Hecate946/reed-case/src/parts/reed_plate.scad

/*
  Parametric implementation of the double-sided tray disclosed in
  US12103755B2, particularly Figs. 1-10 and claims 1-16.

  The patent does not disclose millimeter dimensions. The topology below
  follows the disclosure; dimensions are fitted to the configured reed and
  humidity-pack envelopes in config.scad.

  One complete tray is modeled from two reed faces and one core; the library
  exporter can fuse those regions into one permanently assembled print.
*/

include <../lib/geometry.scad>
include <../lib/hardware.scad>

// i=0 and i=reeds_per_face are virtual passage boundaries supplied by the
// structural side borders, not separate divider walls. Only indices 1..N-1
// have a physical 1.10 mm guide. This removes the redundant outer divider on
// each side and moves the edge wall inward by exactly its former thickness.
function guide_t(i) = i == 0 || i == reeds_per_face ? 0 : tray_guide_t;
function guide_x(i) = i == 0
                    ? -tray_passage_field_w / 2
                    : i == reeds_per_face
                    ? tray_passage_field_w / 2
                    : -tray_passage_field_w / 2 +
                      i * reed_slot_clear_w +
                      (i - 0.5) * tray_guide_t;
function lane_x(i) = -tray_passage_field_w / 2 +
                     reed_slot_clear_w / 2 +
                     i * (reed_slot_clear_w + tray_guide_t);
function aperture_column_pitch() = min(tray_air_column_pitch,
                                       reed_slot_clear_w / 3.7);
// The reed heel line, and therefore the tip stop, is now referenced directly
// to the tray edge. The aperture field is derived from those two lines rather
// than the other way round, which is what lets the field run nearly the full
// passage length as it does in the reference photographs.
// The reed is located from the tip border inwards. The border is a wall of
// tray_border_w sitting at the tray edge, matching the two side frames, so
// the tip end reads as the same narrow band they do instead of a wide flat
// lip. Slack collects at the open heel end, which is where you reach in to
// lift a reed out anyway.
function tip_stop_outer_y() = tray_d / 2;
function tip_stop_inner_y() = tip_stop_outer_y() - tray_border_w;
function reed_heel_y() = tip_stop_inner_y() - reed_length - reed_tip_clearance;
function aperture_edge_relief_r() = tray_air_hole_d / 2 +
                                    tray_air_edge_relief;
function aperture_start_y() = -tray_d / 2 + aperture_heel_margin +
                              aperture_edge_relief_r();
function aperture_end_y() = tip_stop_inner_y() - aperture_tip_margin -
                            aperture_edge_relief_r();
function aperture_row_pitch() = (aperture_end_y() - aperture_start_y()) /
                                max(tray_air_rows - 1, 1);
function aperture_y(row) = aperture_start_y() + row * aperture_row_pitch();
function rail_start_y() = aperture_start_y() - aperture_row_pitch() / 2;
function rail_end_y() = (aperture_y(rail_rows - 1) +
                         aperture_y(rail_rows)) / 2;
function reed_plane_front_y() = aperture_start_y() -
                                 tray_air_hole_d / 2 -
                                 tray_air_edge_relief -
                                 tray_reed_plane_edge_margin;
// Digits sit centred on the height of the tip-stop wall.
function lane_number_z() = tray_face_t + tray_guide_h / 2;
function reed_center_y() = (reed_heel_y() + tip_stop_inner_y()) / 2;
function guide_wall_start_y() = guide_walls_full_length
                              ? -tray_d / 2 - epsilon
                              : reed_plane_front_y();
function ventilation_field_half_w() =
    abs(lane_x(0)) +
    (tray_air_columns - 1) / 2 * aperture_column_pitch() +
    (tray_air_hole_d + 2 * tray_air_edge_relief) / 2 +
    tray_pack_vent_clearance;

// If both optional features are switched back on at once, the rails can start
// ahead of the sheet and print as detached islands. The margin is small even
// at the default row count, so fail loudly rather than ship floating rails.
assert(!(stock_rails_enable && front_plane_cutout_enable) ||
       rail_start_y() >= reed_plane_front_y() + 0.50,
       str("Stock rails would begin ", reed_plane_front_y() - rail_start_y(),
           " mm ahead of the reed-facing sheet. Increase tray_air_rows, ",
           "reduce tray_reed_plane_edge_margin, or leave ",
           "front_plane_cutout_enable off."));

module patent_face_outline_2d() {
    // A plain rounded rectangle. The magnet pockets are buried inside the
    // side borders now, so there are no ears protruding past this outline.
    offset(r = tray_body_corner_r)
        square([tray_body_w - 2 * tray_body_corner_r,
                tray_d - 2 * tray_body_corner_r], center = true);
}

module patent_platform(h) {
    linear_extrude(height = h) patent_face_outline_2d();
}

module patent_ventilation_apertures_2d(hole_d = tray_air_hole_d) {
    // Physical tray: 22 rows of three small apertures in each passage.
    for (i = [0 : reeds_per_face - 1],
         row = [0 : tray_air_rows - 1],
         col = [0 : tray_air_columns - 1]) {
        x_offset = (col - (tray_air_columns - 1) / 2) *
                   aperture_column_pitch();
        translate([lane_x(i) + x_offset, aperture_y(row)])
            circle(d = hole_d, $fn = is_library_fdm ? 16 : ($preview ? 16 : 24));
    }
}

module patent_front_plane_cutout_2d() {
    // Optional. The reference tray edge is solid above and below the humidity
    // pack mouth, so this is disabled by default; set
    // front_plane_cutout_enable = true in config.scad to restore the open
    // insertion end. The outer-frame strips and corner ears stay full length
    // for stiffness either way.
    if (front_plane_cutout_enable) {
        left_inner_x = guide_x(0) + guide_t(0) / 2;
        right_inner_x = guide_x(reeds_per_face) -
                        guide_t(reeds_per_face) / 2;
        front_y = -tray_d / 2 - epsilon;
        back_y = reed_plane_front_y();

        assert(back_y > -tray_d / 2,
               "Reed-plane margin extends beyond the tray outline");

        translate([(left_inner_x + right_inner_x) / 2,
                   (front_y + back_y) / 2])
            square([right_inner_x - left_inner_x,
                    back_y - front_y], center = true);
    }
}

module patent_lane_number_engraving(first_lane = 1) {
    // Engraved passage numbers on the vertical inner face of the reed tip
    // stop, one per passage, reading upright when the open tray is viewed
    // from the heel end.
    //
    // rotate([90, 0, 0]) maps the glyph's own +x onto world +X and its +y
    // onto world +Z, which is what an observer at -Y reads as left-to-right
    // and upright. That same rotation sends the extrusion to -Y, so the
    // block is placed one depth proud of the wall and cuts back into it.
    if (lane_numbers_enable)
        for (i = [0 : reeds_per_face - 1])
            translate([lane_x(i),
                       tip_stop_inner_y() + lane_number_depth,
                       lane_number_z()])
                rotate([90, 0, 0])
                    linear_extrude(height = lane_number_depth + epsilon)
                            text(str(i + first_lane),
                                 size = lane_number_size,
                                 font = lane_number_font,
                                 halign = "center",
                                 valign = "center",
                                 $fn = is_library_fdm ? 16 : ($preview ? 16 : 32));
}

module patent_perforated_layer(z, h, hole_d, outline_inset = 0) {
    // Keep the perforations as ordinary 2D boolean holes before extrusion.
    // This is substantially faster and more reliable in OpenSCAD 2021 than
    // encoding hundreds of hole loops into one giant polygon path.  It also
    // produces a normal slicer-friendly manifold instead of spending minutes
    // in CGAL triangulation during each STL export.
    translate([0, 0, z])
        linear_extrude(height = h, convexity = 10)
            difference() {
                offset(delta = -outline_inset) patent_face_outline_2d();
                patent_ventilation_apertures_2d(hole_d);
                patent_front_plane_cutout_2d();
            }
}

module patent_perforated_platform() {
    // Production keeps the tiny stepped relief around every ventilation hole.
    // A 0.18 mm rim relief is below what a typical 0.4 mm-nozzle library FDM
    // printer can reproduce consistently, while it makes OpenSCAD 2021 spend
    // several extra minutes unioning hundreds of tiny loops.  The library
    // profile therefore exports the SAME 1.60 mm functional holes as one flat
    // sheet.  Nothing affecting reed, Boveda, band, or magnet fit changes.
    if (is_library_fdm) {
        patent_perforated_layer(0, tray_face_t, tray_air_hole_d, 0);
    } else {
        relief_step_h = tray_air_edge_relief_h / tray_air_edge_steps;
        core_h = tray_face_t - tray_air_edge_relief_h;

        union() {
            patent_perforated_layer(0, core_h + epsilon, tray_air_hole_d, 0);
            for (step = [0 : tray_air_edge_steps - 1])
                patent_perforated_layer(
                    core_h + step * relief_step_h - epsilon,
                    relief_step_h + 2 * epsilon,
                    tray_air_hole_d + 2 * tray_air_edge_relief *
                        (step + 1) / tray_air_edge_steps,
                    tray_platform_top_chamfer *
                        (step + 1) / tray_air_edge_steps
                );
        }
    }
}

module patent_guide_walls() {
    // In the reference photographs the dividers run the whole length of the
    // tray. They are extruded as one 2D profile intersected with the tray
    // outline, so the ends follow the rounded corners instead of hanging over
    // them, and the whole set is a single cheap extrusion.
    start_y = guide_wall_start_y();
    end_y = tip_stop_inner_y() + epsilon;

    translate([0, 0, tray_face_t - tray_feature_fuse_overlap])
        union()
            // The side borders are the outer walls; only make the N-1
            // dividers that actually separate adjacent reed passages.
            for (i = [1 : reeds_per_face - 1])
                intersection() {
                    linear_extrude(height = tray_guide_h + tray_feature_fuse_overlap)
                        patent_face_outline_2d();
                    top_chamfered_extrude(tray_guide_h + tray_feature_fuse_overlap,
                                          tray_wall_top_chamfer)
                        translate([guide_x(i), (start_y + end_y) / 2])
                            square([guide_t(i), end_y - start_y],
                                   center = true);
                }
}

module patent_guide_end_runout() {
    // Cutting solid that takes every raised feature down to the floor over
    // the last guide_end_taper millimetres of the open heel end.
    //
    // The quarter-round is intentionally oriented so the visible profile is
    // tangent to the FLOOR at the open heel and turns upward into the full
    // wall inboard. This is the opposite curvature from the previous
    // prototype: instead of looking like a rounded nose dropping into the
    // opening, the wall now rises smoothly out of the reed plane.
    //
    // guide_end_taper == tray_guide_h gives a true circular quarter round.
    L = guide_end_taper;
    h = tray_guide_h;
    y0 = -tray_d / 2 - epsilon;
    z0 = tray_face_t;
    z_top = z0 + h + 1.0;
    steps = is_library_fdm ? 16 : ($preview ? 10 : 24);
    span = tray_w + 20;

    if (L > 0)
        translate([-span / 2, 0, 0])
            rotate([0, 90, 0])
                linear_extrude(height = span)
                    polygon(concat(
                        [[z0 - 1.0, y0 - 1.0], [z_top, y0 - 1.0],
                         [z_top, y0 + L]],
                        [for (s = [steps : -1 : 0])
                            let (u = s / steps)
                            [z0 + h * (1 - sqrt(max(1 - u * u, 0))),
                             y0 + L * u]],
                        [[z0 - 1.0, y0]]
                    ));
}

module patent_longitudinal_stock_rails() {
    // Fig. 4 element 152. Two rounded rails per passage, each sitting midway
    // between adjacent aperture columns so it runs tangent to the softened
    // hole rims rather than across them. They begin half a row pitch below
    // the first aperture, at the heel edge, and stop halfway between rows 11
    // and 12 - the 11.5th row - covering exactly half of the 22-row field.
    //
    // The profile is a hull of two flattened spheres, which gives a rounded
    // crown and domed ends in one cheap operation.
    end_radius = rail_w / 2;

    if (stock_rails_enable)
    for (i = [0 : reeds_per_face - 1], side = [-1, 1])
        hull()
            for (y = [rail_start_y() + end_radius,
                      rail_end_y() - end_radius])
                translate([lane_x(i) +
                           side * aperture_column_pitch() / 2,
                           y,
                           tray_face_t])
                    scale([1, 1, rail_h / end_radius])
                        sphere(d = rail_w, $fn = is_library_fdm ? 16 : ($preview ? 16 : 32));
}

module patent_reed_tip_stop() {
    // The third border. Same construction as the side frames: a plain
    // rectangle of tray_border_w, run out to the tray edge and intersected
    // with the body outline so the two ends pick up the corner radius and
    // meet the side frames in a closed U.
    inner_y = tip_stop_inner_y();

    assert(tray_border_w >= lane_number_depth + 1.0,
           "Tip border is too thin to carry the engraved numbers");

    translate([0, 0, tray_face_t - tray_feature_fuse_overlap])
        intersection() {
            linear_extrude(height = tray_guide_h + tray_feature_fuse_overlap)
                patent_face_outline_2d();
            top_chamfered_extrude(tray_guide_h + tray_feature_fuse_overlap,
                                  tray_wall_top_chamfer)
                translate([0, inner_y + tray_border_w / 2 + epsilon])
                    square([tray_body_w + 20,
                            tray_border_w + 2 * epsilon], center = true);
        }
}

module patent_outer_side_walls() {
    // The structural side frames now ARE the outer walls of lanes 1 and N.
    // Their inner faces sit exactly where the inner faces of the old outer
    // divider walls sat. That removes one redundant 1.60 mm wall per side
    // while preserving lane width, magnet protection and the rounded outline.
    passage_edge = tray_passage_field_w / 2;
    side_frame_w = tray_body_w / 2 - passage_edge;

    assert(side_frame_w > 0,
           "Passage field leaves no room for a side frame");

    translate([0, 0, tray_face_t - tray_feature_fuse_overlap])
        union()
            for (x = [-1, 1])
                intersection() {
                    linear_extrude(height = tray_guide_h + tray_feature_fuse_overlap)
                        patent_face_outline_2d();
                    top_chamfered_extrude(tray_guide_h + tray_feature_fuse_overlap,
                                          tray_wall_top_chamfer)
                        translate([x * (passage_edge +
                                        side_frame_w / 2), 0])
                            square([side_frame_w,
                                    tray_d + 2 * epsilon], center = true);
                }
}

module patent_magnet_apertures() {
    for (x = [-1, 1], y = [-1, 1])
        translate([x * tray_magnet_x, y * tray_magnet_y,
                   tray_face_t + tray_guide_h -
                   tray_magnet_h - magnet_h_clearance])
            magnet_pocket();
}

function band_groove_r() = elastic_band_d / 2 + elastic_band_clearance;
function band_groove_z() = tray_face_t + tray_guide_h -
                           band_groove_r() - elastic_band_seat_depth;
function band_y(gap) = aperture_y(gap - 1);

module patent_band_notches() {
    // A half-round seat for round elastic cord, swept across the whole tray
    // so every divider, both side borders and the tip border get the same
    // groove and the cord runs dead straight.
    //
    // The groove centre is elastic_band_seat_depth below a plain half-round,
    // so the cord sits about 70% buried and cannot roll off the wall tops,
    // while the mouth stays wider than the cord and needs no undercut.
    //
    // band_y() takes a 1-indexed row gap: 8.5 is between holes 8 and 9,
    // counting apertures from the heel end.
    for (gap = elastic_band_row_gaps) {
        translate([-tray_w / 2 - epsilon, band_y(gap), band_groove_z()])
            rotate([0, 90, 0])
                cylinder(r = band_groove_r(),
                         h = tray_w + 2 * epsilon,
                         $fn = is_library_fdm ? 20 : ($preview ? 24 : 48));
        // Square off everything above the seat so the mouth is open to the
        // top face instead of leaving a lip the cord has to snap past.
        translate([0, band_y(gap),
                   band_groove_z() + (tray_guide_h + 1) / 2])
            cube([tray_w + 2 * epsilon,
                  2 * band_groove_r(),
                  tray_guide_h + 1], center = true);
    }
}

module patent_pack_stop_ribs() {
    // Full-height humidity-pack stop ribs live in the CENTER CORE, not on the
    // printable reed faces. This is deliberately a printability feature:
    // face A and face B now have completely flat backs at Z=0 and can be
    // printed reed-side-up directly on the build plate with no supports.
    //
    // The ribs start at the heel bridge, so they are fused to the U-shaped
    // core and cannot become loose islands. Their final volume is identical
    // to the two old half-ribs after assembly; it is simply assigned to the
    // support-friendly part instead.
    rib_start_y = -tray_d / 2;
    rib_end_y = tray_pack_stop_y;
    rib_length = rib_end_y - rib_start_y;

    for (i = [1 : reeds_per_face - 1])
        translate([guide_x(i), (rib_start_y + rib_end_y) / 2,
                   tray_core_h / 2])
            cube([tray_pack_support_w, rib_length,
                  tray_core_h], center = true);
}

module behn_tray_face(first_lane = 1) {
    union() {
        patent_perforated_platform();
        difference() {
            union() {
            patent_guide_walls();
            patent_outer_side_walls();
            patent_longitudinal_stock_rails();
            patent_reed_tip_stop();
            }
            patent_guide_end_runout();
            patent_band_notches();
            patent_magnet_apertures();
            patent_lane_number_engraving(first_lane);
        }
    }
}

module behn_tray_core() {
    // The channel is wide enough to expose even the outer edges of the
    // chamfered ventilation holes, not merely wide enough for the pack.
    cavity_w = max(boveda_w + 2 * boveda_clearance,
                   2 * ventilation_field_half_w());
    side_rail_w = (tray_body_w - cavity_w) / 2;
    mouth_cap_r = side_rail_w / 2;
    cavity_start_y = -tray_d / 2 + tray_core_heel_bridge_d;
    cap_center_y = tray_d / 2 - mouth_cap_r;

    assert(side_rail_w >= tray_core_side_wall_min,
           "Humidity channel leaves too little material in the core side rails");
    assert(cap_center_y > cavity_start_y,
           "Core is too short for a semicircular humidity-pack mouth cap");

    // Build the core positively as a U-frame instead of subtracting circular
    // bites from a rectangular frame.  Each open leg therefore terminates in
    // a TRUE SEMICIRCULAR CAP: the outer and inner edges have the same radius
    // and flow continuously into one another, like ().  This avoids the old
    // concave 'bite taken out of the corner' appearance at the pack mouth.
    union() {
        linear_extrude(height = tray_core_h, convexity = 10)
            intersection() {
                patent_face_outline_2d();
                union() {
                // Narrow heel bridge keeps the core one connected print.
                translate([0,
                           -tray_d / 2 + tray_core_heel_bridge_d / 2])
                    square([tray_body_w,
                            tray_core_heel_bridge_d], center = true);

                // Two straight rails with pill/semicircular open ends.
                for (side = [-1, 1]) {
                    rail_x = side * (cavity_w / 2 + side_rail_w / 2);

                    // Straight portion; overlaps the heel bridge slightly so
                    // the exported STL is unequivocally one fused solid.
                    translate([rail_x,
                               (cavity_start_y + cap_center_y) / 2])
                        square([side_rail_w,
                                cap_center_y - cavity_start_y + 2 * epsilon],
                               center = true);

                    // Equal-radius cap on both sides of the rail end.
                    translate([rail_x, cap_center_y])
                        circle(r = mouth_cap_r,
                               $fn = is_library_fdm ? 32 : ($preview ? 32 : 64));
                }
                }
            }

        // The full-height pack-stop ribs are part of this flat-printing core.
        patent_pack_stop_ribs();
    }
}

// Passages 1..N. Hardware pockets are identical to face B.
module behn_tray_face_a() { behn_tray_face(1); }

// Passages N+1..2N. Geometry matches face A except for numbering; the final
// magnet/steel assignment is intentionally not encoded in the printed part.
module behn_tray_face_b() { behn_tray_face(reeds_per_face + 1); }

// Positive overlap used only by the monolithic export. The three-piece
// construction can meet at exact planes, but a one-piece STL should contain
// actual shared volume so slicers cannot interpret the interfaces as shells.
tray_monolithic_fuse = 0.15;

module behn_tray_interface_fusers(overlap = tray_monolithic_fuse) {
    // Copy a thin slice of the core through each mating face. These slices
    // occupy material that is already inside the face sheets, so they create
    // a true boolean union without changing the external dimensions or the
    // Boveda opening.
    translate([0, 0, -overlap])
        intersection() {
            behn_tray_core();
            translate([-tray_body_w, -tray_d, 0])
                cube([2 * tray_body_w, 2 * tray_d, overlap]);
        }

    translate([0, 0, overlap])
        intersection() {
            behn_tray_core();
            translate([-tray_body_w, -tray_d, tray_core_h - overlap])
                cube([2 * tray_body_w, 2 * tray_d, overlap]);
        }
}


module behn_tray_core_monolithic() {
    // Same XY geometry as the normal core, extended 0.15 mm into each face.
    // This does NOT narrow the Boveda tunnel; only the solid core rails/ribs
    // enter the face sheets. The overlap guarantees the one-file library STL
    // slices as one permanently fused physical part.
    translate([0, 0, -tray_monolithic_fuse])
        scale([1, 1,
               (tray_core_h + 2 * tray_monolithic_fuse) / tray_core_h])
            behn_tray_core();
}

module behn_tray_one_piece() {
    // Finished, permanently fused double-sided tray. Pre-render each major
    // region into a clean CGAL mesh before the final union. This keeps the
    // final Boolean to three modest polyhedra instead of asking CGAL to
    // re-evaluate every ventilation-hole primitive at once.
    union() {
        render(convexity = 20) behn_tray_core_monolithic();
        translate([0, 0, tray_core_h])
            render(convexity = 20) behn_tray_face_a();
        rotate([0, 180, 0])
            render(convexity = 20) behn_tray_face_b();
    }
}

module behn_tray_one_piece_library_oriented() {
    // A 45-degree long-edge orientation avoids the ~72 mm horizontal bridge
    // over the Boveda tunnel that a flat monolithic print would create. It
    // also turns the two outward reed faces into ~45-degree overhangs. The
    // slicer should add a generous brim, but should NOT auto-lay-flat this STL.
    a = 45;
    lift = (tray_body_w * sin(a) + tray_total_h * cos(a)) / 2;
    translate([0, 0, lift])
        rotate([0, a, 0])
            translate([0, 0, -tray_core_h / 2])
                behn_tray_one_piece();
}

module behn_tray() {
    color([0.16, 0.18, 0.21]) behn_tray_core();
    color([0.20, 0.22, 0.25])
        translate([0, 0, tray_core_h]) behn_tray_face_a();
    // The lower face is rotated about Y, not mirrored: a reflection is not a
    // physical operation. The rotation keeps the reed-tip end at the tip end
    // and the engraved digits reading correctly from below.
    color([0.20, 0.22, 0.25])
        rotate([0, 180, 0]) behn_tray_face_b();
}

// Backward-compatible aliases for the original preview names.
module reed_plate() { behn_tray_face_a(); }
