Hecate946/reed-case/frozen/compact_size8_20260831/src/export.scad

/* CLI export entry point. Prefer the Makefile commands in the project root. */

part = is_undef(part) ? "case_open" : part;

include <config.scad>
include <assembly.scad>

render_selected(part);
